MOSH-Insa-Toulouse/2025-2026-4GP-NGUYEN-PHAN-GAMBOA/Images/Model_3D.jpg

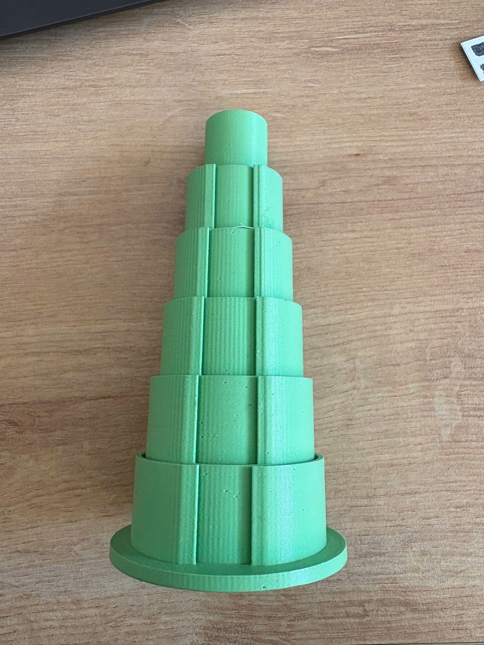
Images/Model_3D.jpg
