MOSH-Insa-Toulouse/2025-2026-4GP-NGUYEN-PHAN-GAMBOA/KiCad/KiCAD_1/Component library/Dip_ic_on_sip_socket/models3d/DIP/DIP-24 on SCSL-12 x2.step

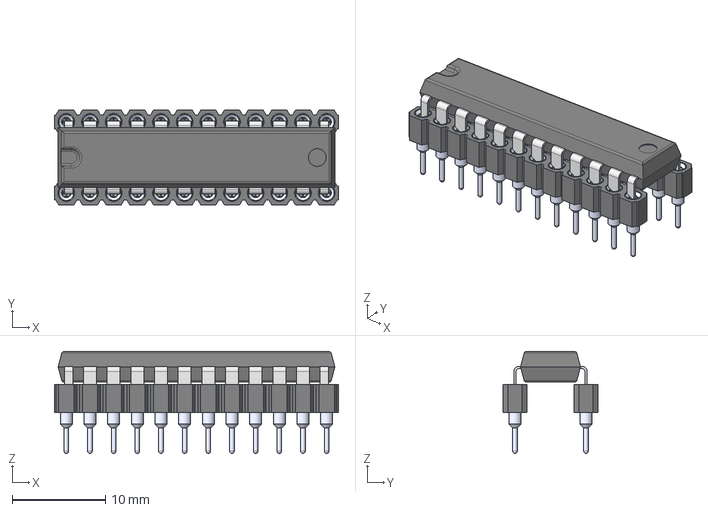
[picture p47: CAD file, 2026-02-25]
KiCad/KiCAD_1/Component library/Dip_ic_on_sip_socket/models3d/DIP/DIP-24 on SCSL-12 x2.step
30.5 x 10.2 x 10.9 mm
SCSL x 2
DIP
