MOSH-Insa-Toulouse/2025-2026-4GP-NGUYEN-PHAN-GAMBOA/KiCad/KiCAD_1/Component library/Pin_header_female_2_54mm/12-Pin Header - Female - 2.54mm.step

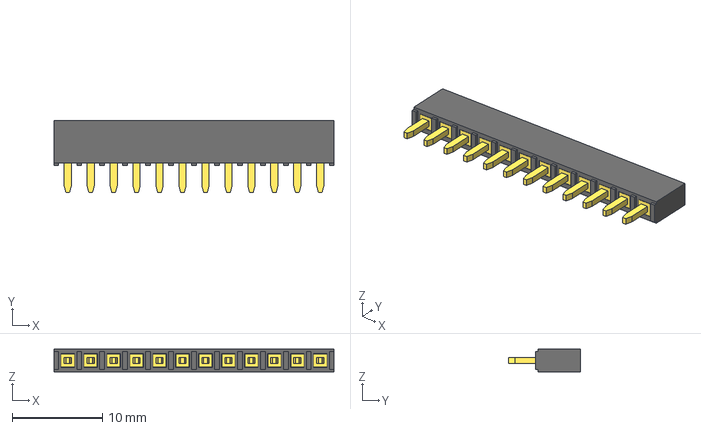
[picture p60: CAD file, 2026-02-25]
KiCad/KiCAD_1/Component library/Pin_header_female_2_54mm/12-Pin Header - Female - 2.54mm.step
31.0 x 8.00 x 2.50 mm
