MOSH-Insa-Toulouse/2025-2026-4GP-NGUYEN-PHAN-GAMBOA/LTSpice/circuit_amplificateur/Circuit.asc

C1: cap; 100n
C2: cap; 100n
C3: cap; 1p
C4: cap; 1µ
R1: res; 100K
R2: res; {R2}
R3: res; 100K
R5: res; 10K
R6: res; 1k
U1: LTC1050
V1: voltage; 5
V2: voltage; SINE(0 325 50)
V3: voltage; PULSE(0 1 0.2 0.1 0.1 2); AC 1
X2: capteur_graphite
Named nets: 0, ADC
.param G0 10n
.step param R2 0.5k 2k 0.5k
.param G1 10n
.tran 10
;ac dec 100 1 1G
