MOSH-Insa-Toulouse/2025-2026-4GP-NGUYEN-PHAN-GAMBOA/LTSpice/circuit_amplificateur/capteur_graphite.asc

B1: bi; I=V(cp,cn)*({G0}+v(gc,gn)*{G1})
C1: cap; 200µ
R1: res; 1k
Named nets: gp, gn, cp, gc, cn
