MOSH-Insa-Toulouse/2025-2026-4GP-NGUYEN-PHAN-GAMBOA/Arduino/digipot.cpp

#include "digipot.h"
#include <SPI.h>

const byte csPin           = 10;      // MCP42100 chip select pin
const int  maxPositions    = 256;     // wiper can move from 0 to 255 = 256 positions
const long rAB             = 10000;//92500;   // 100k pot resistance between terminals A and B, 
                                      // mais pour ajuster au multimètre, je mets 92500
const byte rWiper          = 125;     // 125 ohms pot wiper resistance
const byte pot0            = 0x11;    // pot0 addr // B 0001 0001
const byte pot0Shutdown    = 0x21;    // pot0 shutdown // B 0010 0001

float R2;

static void setPotWiper();

void initDigipot() {
  digitalWrite(csPin, HIGH);
  pinMode(csPin, OUTPUT);
  SPI.begin();
}

static void setPotWiper(int addr, int pos) {
  pos = constrain(pos, 0, 255);            // limit wiper setting to range of 0 to 255
  digitalWrite(csPin, LOW);                // select chip
  SPI.transfer(addr);                      // configure target pot with wiper position
  SPI.transfer(pos);
  digitalWrite(csPin, HIGH);               // de-select chip

  // print pot resistance between wiper and B terminal
  float resistanceWB = ((rAB * pos) / maxPositions ) + rWiper;
  R2 = resistanceWB;
}

void applyGain(int gainLevel) {
/////////////////comment
  setPotWiper(pot0, gainLevel);

}
